studiohsoftware/UNBRICKER/Firmware/uChipSAMD21unbrick/samd21_sam_ba_arduino_mkr1000.bin.h

#ifndef SAMD21_SAM_BA_ARDUINO_MKR1000_BIN_H
#define SAMD21_SAM_BA_ARDUINO_MKR1000_BIN_H

static const unsigned char samd21_sam_ba_arduino_mkr1000_bin[] = {
	0xfc, 0x7f, 0x00, 0x20, 0xd9, 0x0e, 0x00, 0x00, 0x29, 0x04, 0x00, 0x00,
	0x25, 0x04, 0x00, 0x00, 0x00, 0x00, 0x00, 0x00, 0x00, 0x00, 0x00, 0x00,
	0x00, 0x00, 0x00, 0x00, 0x00, 0x00, 0x00, 0x00, 0x00, 0x00, 0x00, 0x00,
	0x00, 0x00, 0x00, 0x00, 0x00, 0x00, 0x00, 0x00, 0x21, 0x04, 0x00, 0x00,
	0x00, 0x00, 0x00, 0x00, 0x00, 0x00, 0x00, 0x00, 0x1d, 0x04, 0x00, 0x00,
	0xa1, 0x03, 0x00, 0x00, 0x10, 0xb5, 0x06, 0x4c, 0x23, 0x78, 0x00, 0x2b,
	0x07, 0xd1, 0x05, 0x4b, 0x00, 0x2b, 0x02, 0xd0, 0x04, 0x48, 0x00, 0xe0,
	0x00, 0xbf, 0x01, 0x23, 0x23, 0x70, 0x10, 0xbd, 0x5c, 0x00, 0x00, 0x20,
	0x00, 0x00, 0x00, 0x00, 0x10, 0x16, 0x00, 0x00, 0x04, 0x4b, 0x10, 0xb5,
	0x00, 0x2b, 0x03, 0xd0, 0x03, 0x49, 0x04, 0x48, 0x00, 0xe0, 0x00, 0xbf,
	0x10, 0xbd, 0xc0, 0x46, 0x00, 0x00, 0x00, 0x00, 0x60, 0x00, 0x00, 0x20,
	0x10, 0x16, 0x00, 0x00, 0x02, 0x4b, 0x18, 0x7e, 0x40, 0x07, 0xc0, 0x0f,
	0x70, 0x47, 0xc0, 0x46, 0x00, 0x08, 0x00, 0x42, 0x10, 0xb5, 0xff, 0xf7,
	0xf5, 0xff, 0x00, 0x28, 0xfb, 0xd0, 0x07, 0x4b, 0x1a, 0x00, 0x19, 0x7e,
	0x49, 0x07, 0xfc, 0xd5, 0x59, 0x8b, 0xc9, 0x07, 0x03, 0xd4, 0x59, 0x8b,
	0x89, 0x07, 0x00, 0xd4, 0x5b, 0x8b, 0x10, 0x8d, 0xc0, 0xb2, 0x10, 0xbd,
	0x00, 0x08, 0x00, 0x42, 0xf8, 0xb5, 0x00, 0x25, 0x06, 0x00, 0x0f, 0x00,
	0x2c, 0x00, 0xff, 0xf7, 0xe3, 0xff, 0x11, 0x4a, 0x13, 0x78, 0x00, 0x2b,
	0x1c, 0xd1, 0xff, 0x21, 0x23, 0x0a, 0x01, 0x40, 0x4b, 0x40, 0x21, 0x02,
	0x0d, 0x4c, 0x5b, 0x00, 0x1c, 0x5b, 0x53, 0x88, 0x4c, 0x40, 0xa4, 0xb2,
	0x00, 0x2b, 0x02, 0xd1, 0x12, 0x79, 0x00, 0x2a, 0x06, 0xd0, 0x30, 0x70,
	0x01, 0x36, 0x80, 0x2f, 0x02, 0xd1, 0x05, 0x4a, 0x01, 0x3b, 0x53, 0x80,
	0x01, 0x35, 0xad, 0xb2, 0xaf, 0x42, 0xde, 0xd1, 0x20, 0x00, 0xf8, 0xbd,
	0x01, 0x24, 0xfb, 0xe7, 0x78, 0x00, 0x00, 0x20, 0xc8, 0x13, 0x00, 0x00,
	0x10, 0xb5, 0x04, 0x00, 0xff, 0xf7, 0xb8, 0xff, 0x20, 0x70, 0x01, 0x20,
	0x10, 0xbd, 0x04, 0x4b, 0xc0, 0xb2, 0x1a, 0x7e, 0xd2, 0x07, 0xfc, 0xd5,
	0x80, 0xb2, 0x18, 0x85, 0x01, 0x20, 0x70, 0x47, 0x00, 0x08, 0x00, 0x42,
	0x00, 0x23, 0xf0, 0xb5, 0x2e, 0x4d, 0x85, 0xb0, 0x07, 0x00, 0x2b, 0x70,
	0x99, 0x42, 0x11, 0xd1, 0x01, 0x33, 0x64, 0x24, 0x2b, 0x71, 0x43, 0x20,
	0xff, 0xf7, 0xe7, 0xff, 0x29, 0x4e, 0xff, 0xf7, 0x91, 0xff, 0x00, 0x28,
	0x0a, 0xd1, 0x00, 0x2e, 0x06, 0xd1, 0x01, 0x3c, 0x00, 0x2c, 0xf2, 0xd1,
	0x20, 0x00, 0x0d, 0xe0, 0x69, 0x80, 0xec, 0xe7, 0x01, 0x3e, 0xf0, 0xe7,
	0x00, 0x2e, 0xf4, 0xd0, 0x01, 0x26, 0xff, 0xf7, 0x87, 0xff, 0x2b, 0x78,
	0x00, 0x2b, 0x03, 0xd0, 0x00, 0x20, 0x28, 0x70, 0x05, 0xb0, 0xf0, 0xbd,
	0xff, 0x23, 0x18, 0x40, 0x01, 0x28, 0x05, 0xd0, 0x04, 0x28, 0x2c, 0xd0,
	0x00, 0x23, 0x01, 0x20, 0x2b, 0x71, 0xf3, 0xe7, 0x02, 0x21, 0x03, 0xa8,
	0xff, 0xf7, 0x88, 0xff, 0x80, 0x21, 0x38, 0x00, 0xff, 0xf7, 0x84, 0xff,
	0x01, 0x90, 0xff, 0xf7, 0x6b, 0xff, 0x00, 0x02, 0x84, 0xb2, 0xff, 0xf7,
	0x67, 0xff, 0x01, 0x9b, 0x24, 0x18, 0xa4, 0xb2, 0xa3, 0x42, 0x09, 0xd1,
	0x02, 0xab, 0x1b, 0x79, 0xb3, 0x42, 0x05, 0xd1, 0xf3, 0x43, 0x02, 0xaa,
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
};

#endif /* SAMD21_SAM_BA_ARDUINO_MKR1000_BIN_H */
